dirq/DiamondMineShimmerCircuit/diamond-mine-shimmer.kicad_sch

## KiCad design diamond-mine-shimmer.kicad_sch (2026-02-22, an earlier design)

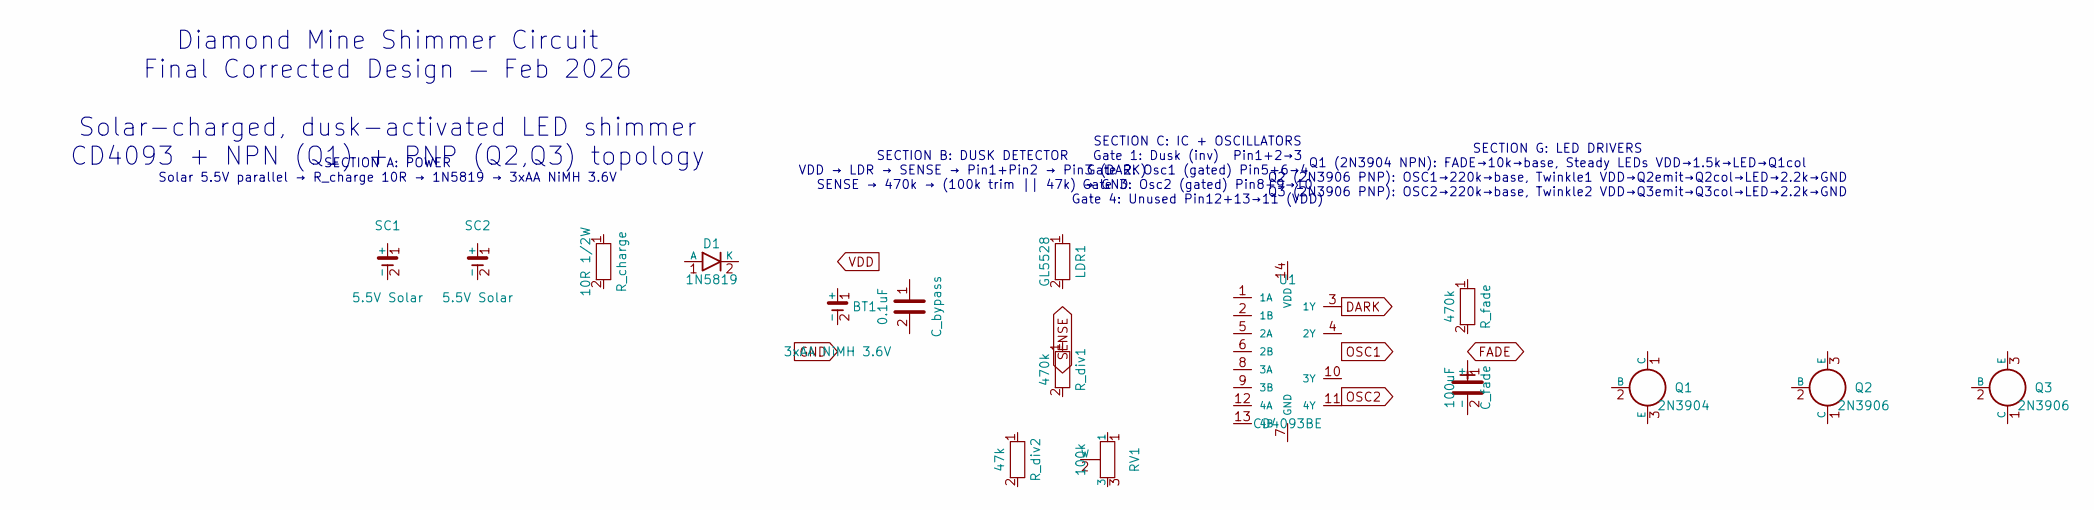
[picture p8: schematic diamond-mine-shimmer.kicad_sch]

Parts:
BT1: 3xAA NiMH 3.6V
C_bypass: 0.1uF
C_fade: 100uF
D1: 1N5819
LDR1: GL5528
Q1: 2N3904
Q2, Q3: 2N3906
RV1: 100k
R_charge: 10R 1/2W
R_div1: 470k
R_div2: 47k
R_fade: 470k
SC1, SC2: 5.5V Solar
U1: CD4093BE

Connections:
DARK: U1.3 (1Y)

Notes on the sheet:
Diamond Mine Shimmer Circuit Final Corrected Design — Feb 2026 Solar-charged, dusk-activated LED shimmer CD4093 + NPN (Q1) + PNP (Q2,Q3) topology
SECTION A: POWER Solar 5.5V parallel → R_charge 10R → 1N5819 → 3xAA NiMH 3.6V
SECTION B: DUSK DETECTOR VDD → LDR → SENSE → Pin1+Pin2 → Pin3 (DARK) SENSE → 470k → (100k trim || 47k) → GND
SECTION C: IC + OSCILLATORS Gate 1: Dusk (inv) Pin1+2→3 Gate 2: Osc1 (gated) Pin5+6→4 Gate 3: Osc2 (gated) Pin8+9→10 Gate 4: Unused Pin12+13→11 (VDD)
SECTION G: LED DRIVERS Q1 (2N3904 NPN): FADE→10k→base, Steady LEDs VDD→1.5k→LED→Q1col Q2 (2N3906 PNP): OSC1→220k→base, Twinkle1 VDD→Q2emit→Q2col→LED→2.2k→GND Q3 (2N3906 PNP): OSC2→220k→base, Twinkle2 VDD→Q3emit→Q3col→LED→2.2k→GND
